LAKSHYA-2005/iot-smart-room-monitoring-and-safety-device/block diagram .jpeg

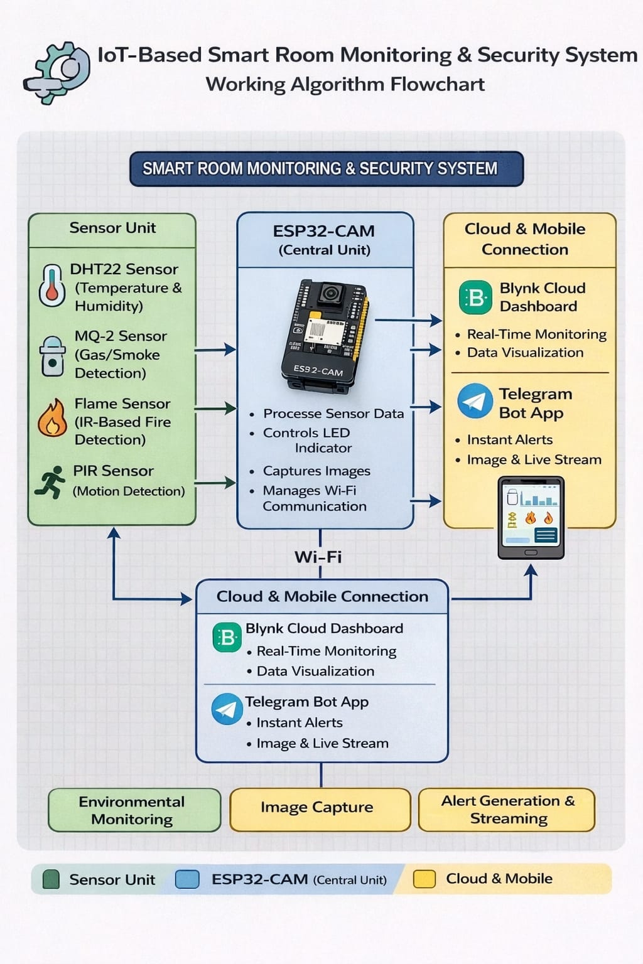
block diagram .jpeg
