LAKSHYA-2005/iot-smart-room-monitoring-and-safety-device/BUZZER 5V.jpeg

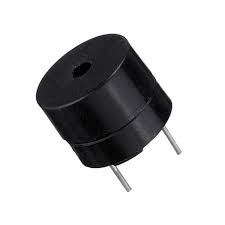
BUZZER 5V.jpeg
