LAKSHYA-2005/iot-smart-room-monitoring-and-safety-device/flowchart .jpeg

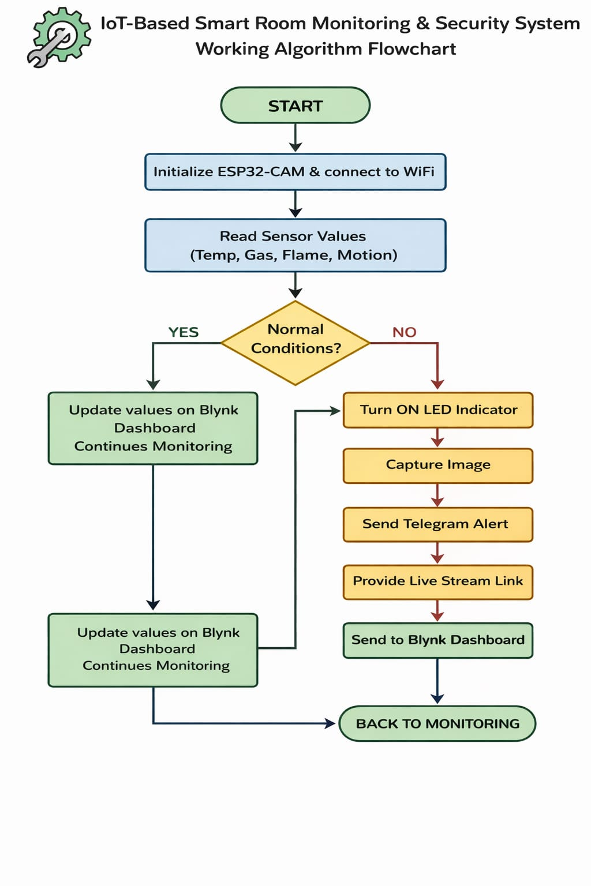
flowchart .jpeg
