LAKSHYA-2005/iot-smart-room-monitoring-and-safety-device/mq-2-smokegas-sensor.jpg

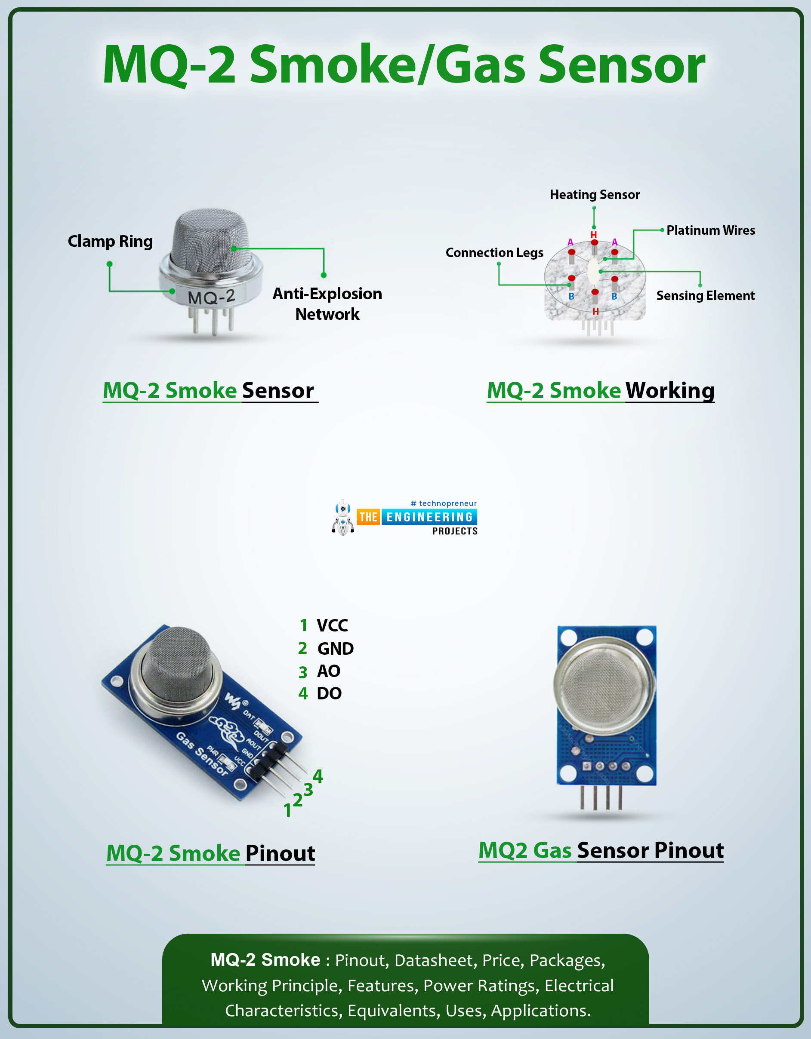
mq-2-smokegas-sensor.jpg
